hzprky/Sharp-EA-129C-Clone/images/EA-129C_final_test.jpg

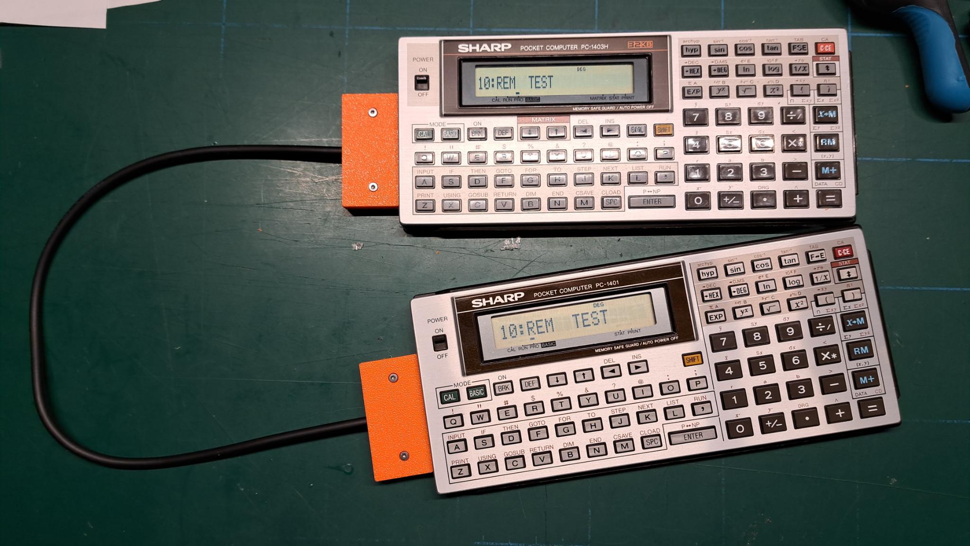
images/EA-129C_final_test.jpg
